joeostrander/gameboy_xl/images/IMG_4544.JPG

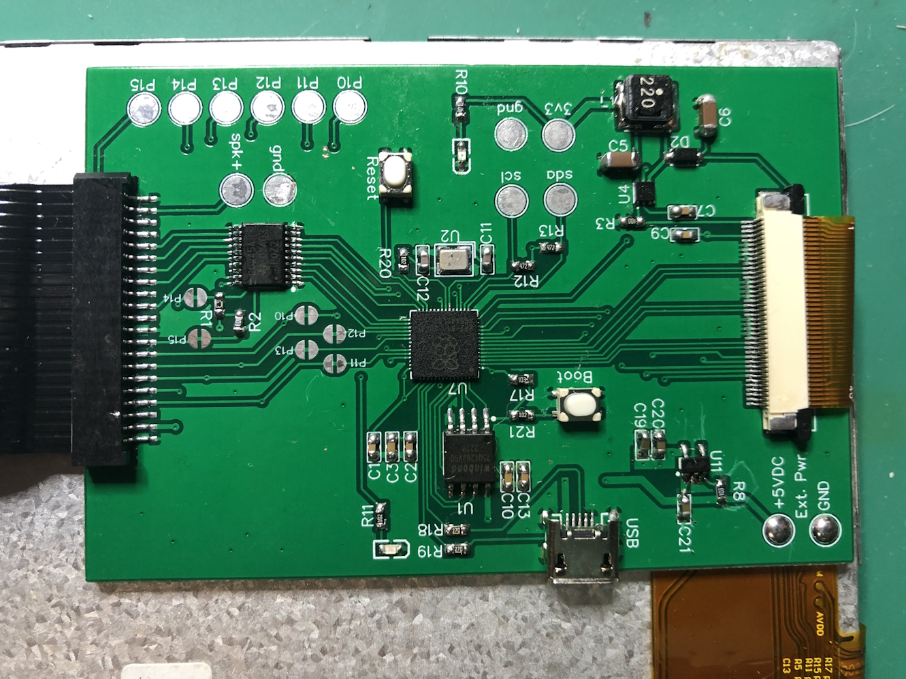
images/IMG_4544.JPG
