joeostrander/gameboy_xl/images/IMG_4554.JPG

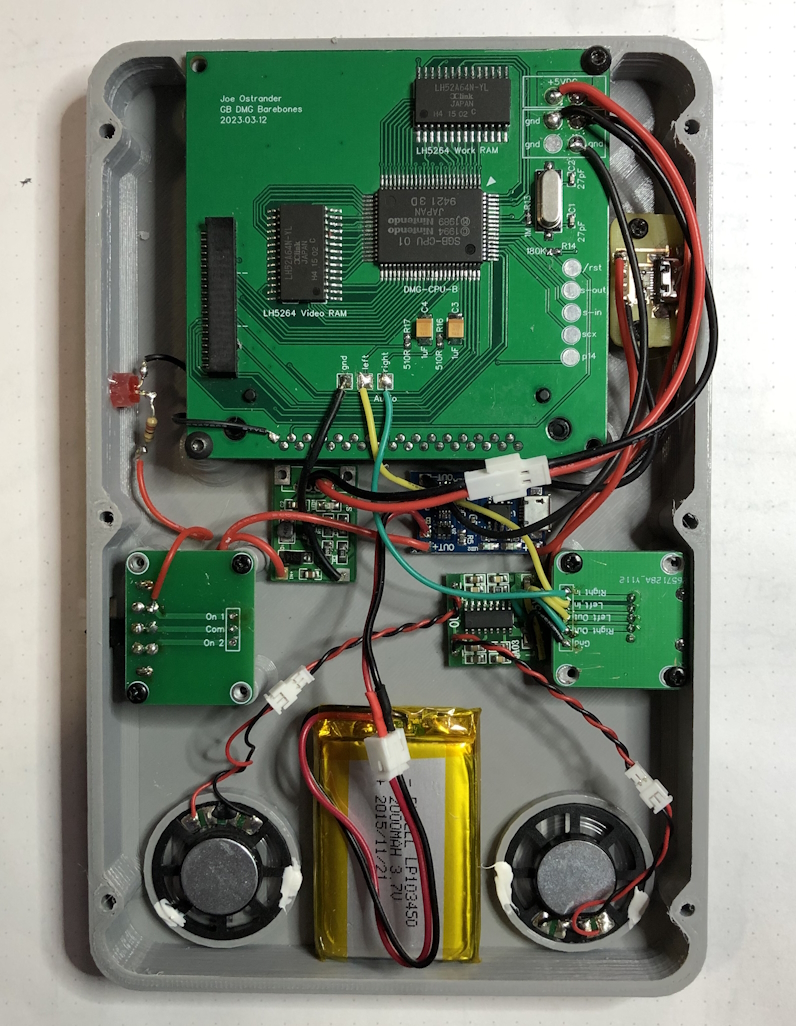
images/IMG_4554.JPG
