joeostrander/gameboy_xl/images/IMG_4557.JPG

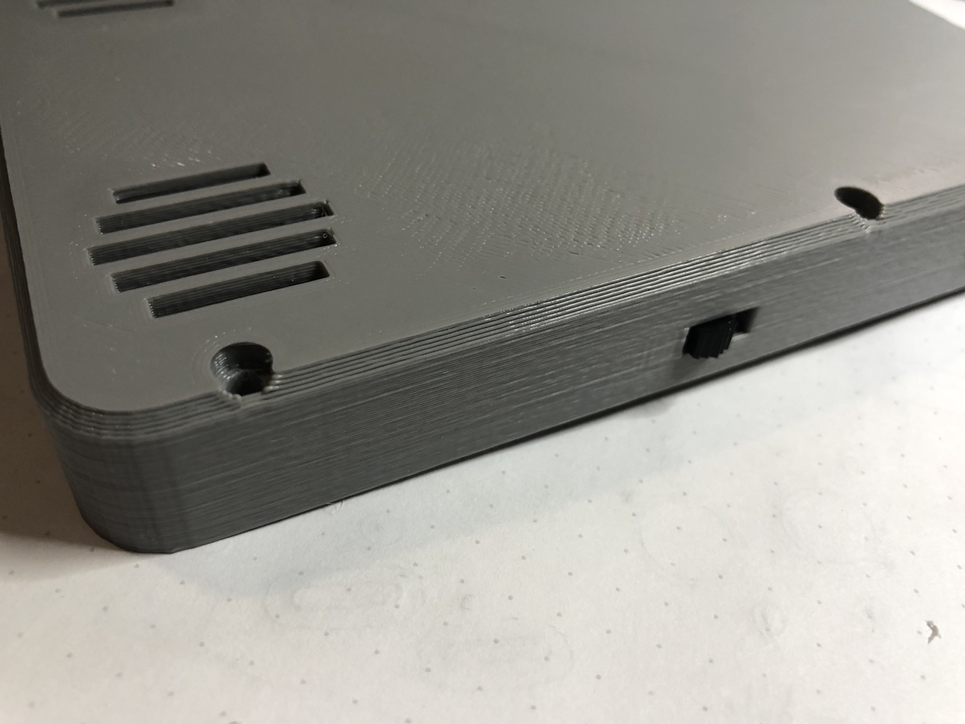
images/IMG_4557.JPG
