joeostrander/gameboy_xl/images/IMG_4558.JPG

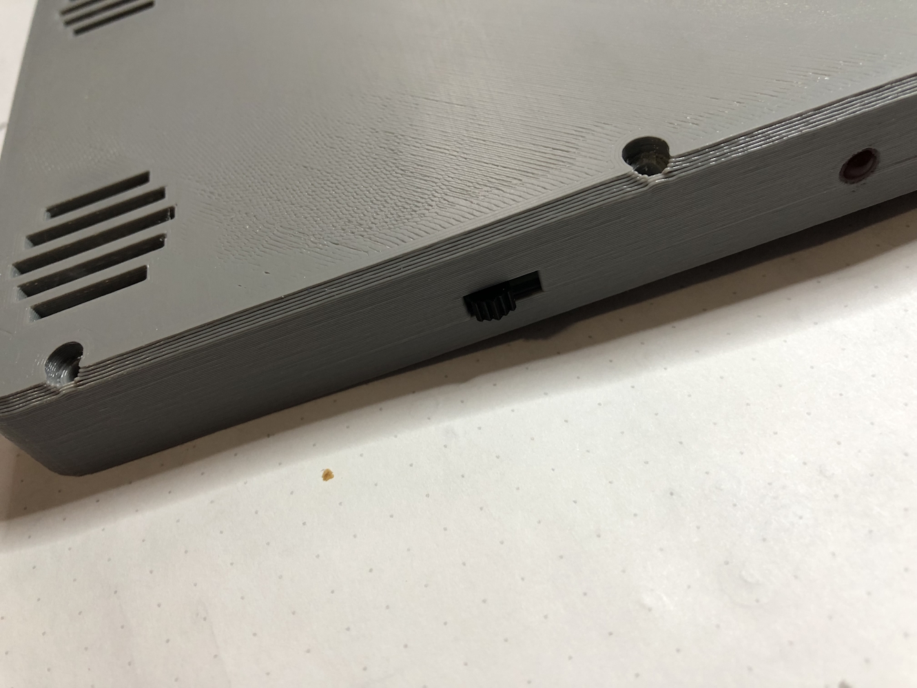
images/IMG_4558.JPG
