joeostrander/gameboy_xl/images/IMG_4560.JPG

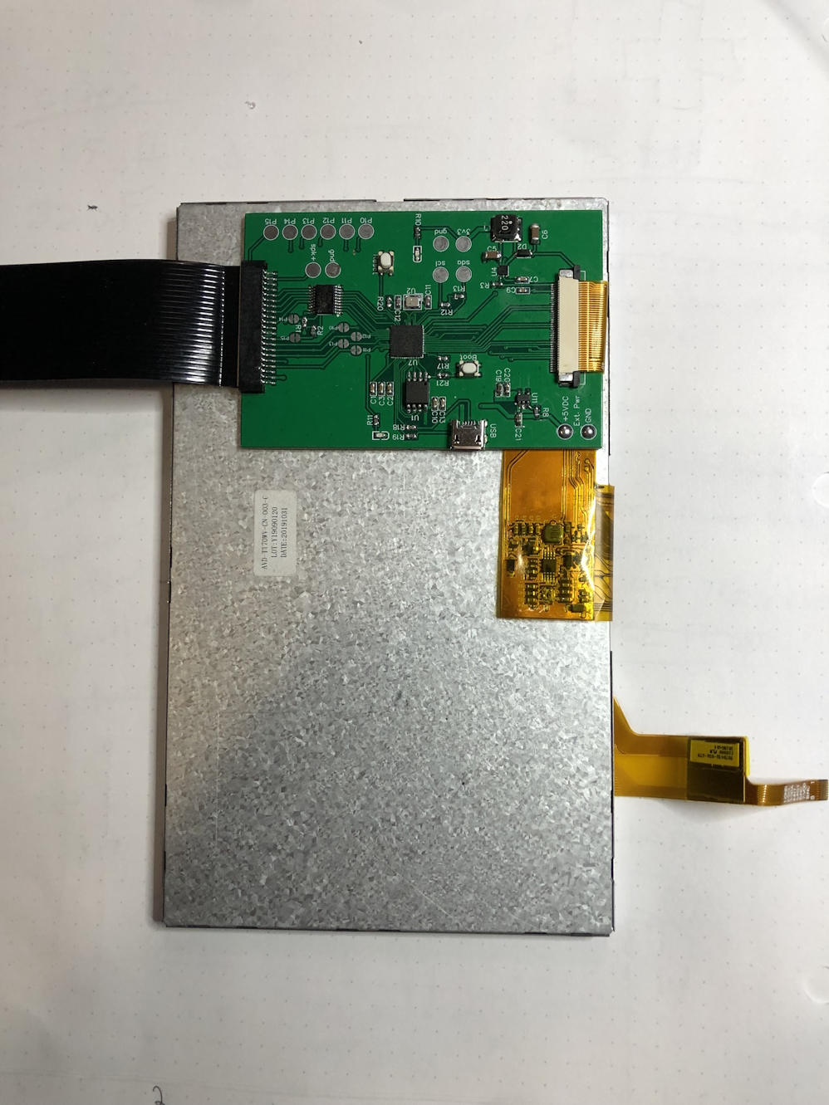
images/IMG_4560.JPG
