joeostrander/gameboy_xl/images/IMG_4566.JPG

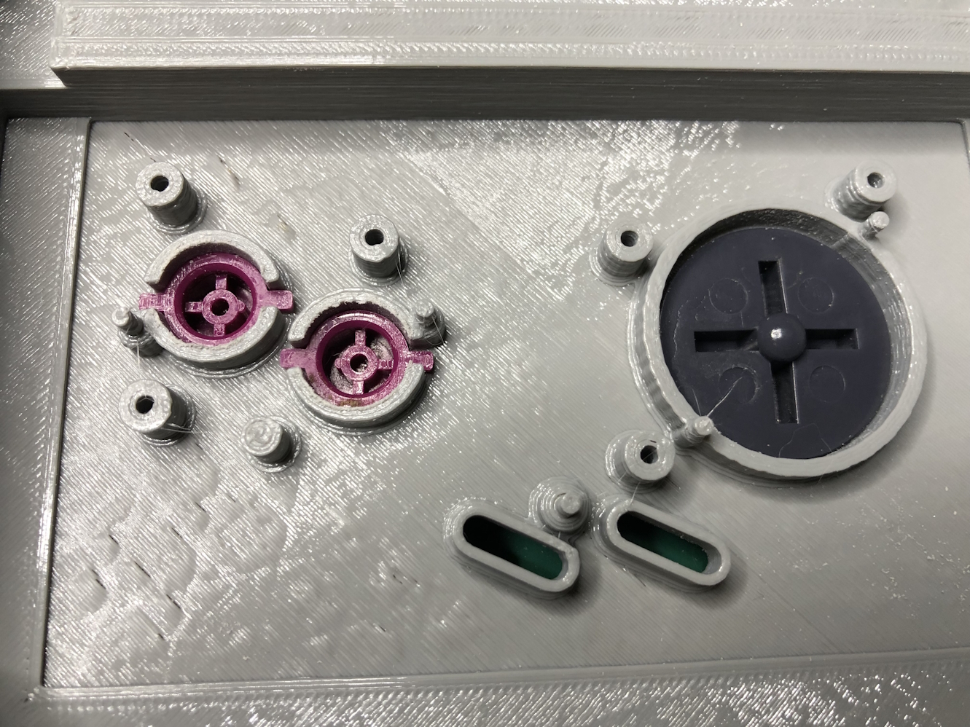
images/IMG_4566.JPG
