joeostrander/gameboy_xl/images/IMG_4568.JPG

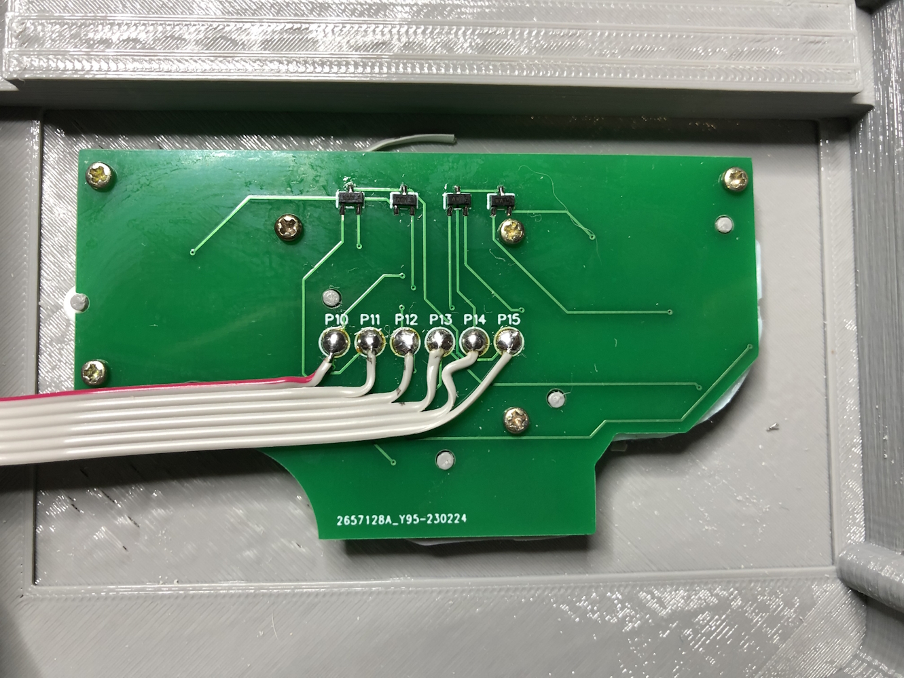
images/IMG_4568.JPG
