joeostrander/gameboy_xl/images/IMG_4569.JPG

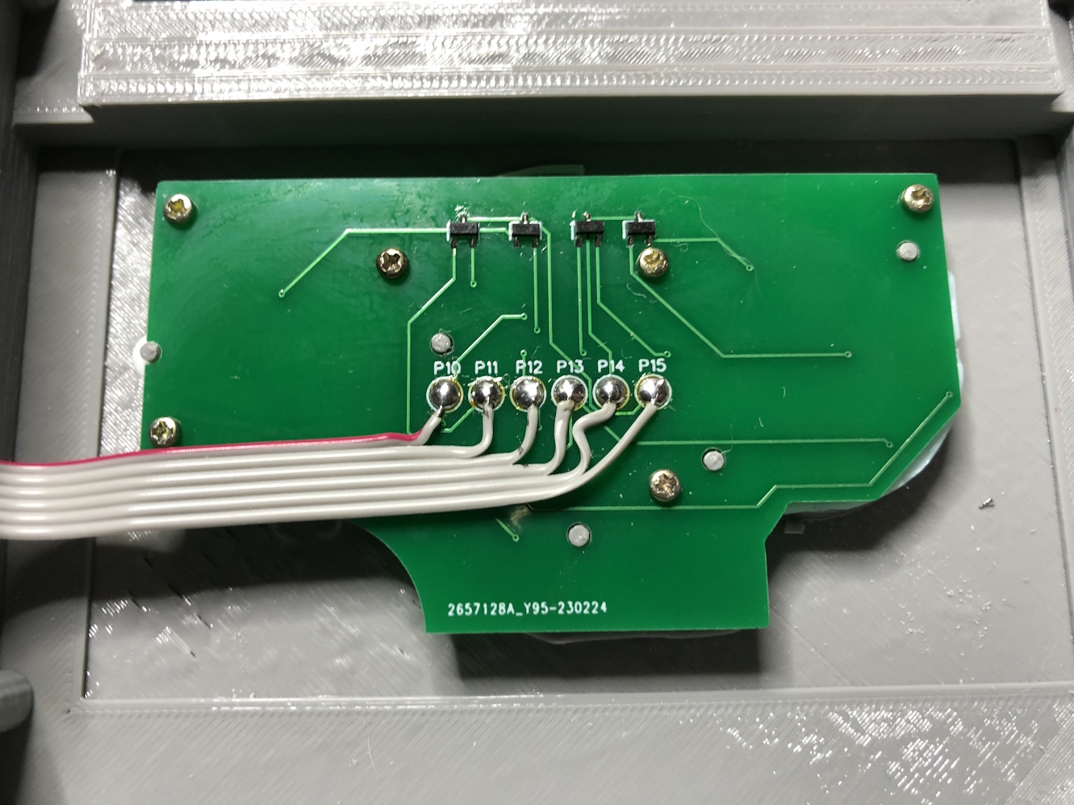
images/IMG_4569.JPG
