joeostrander/gameboy_xl/images/IMG_4572.JPG

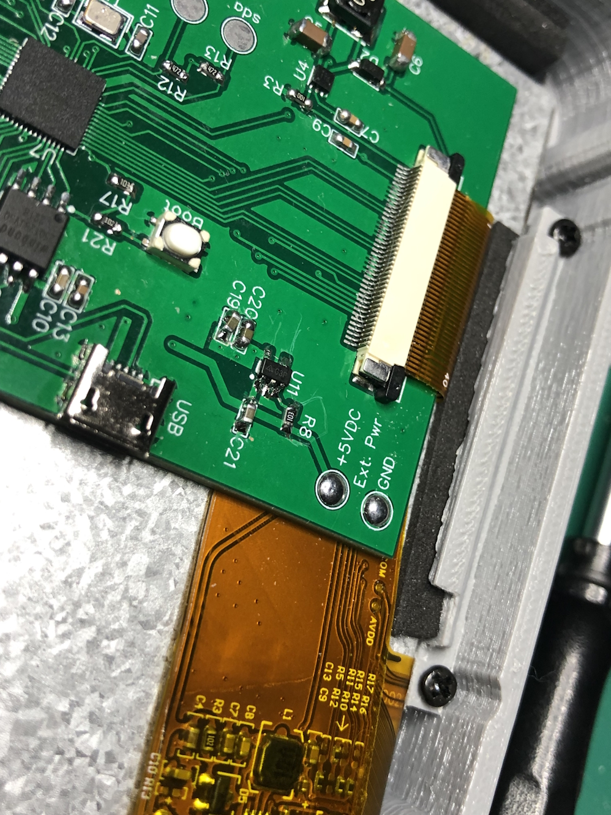
images/IMG_4572.JPG
