joeostrander/gameboy_xl/images/IMG_4573.JPG

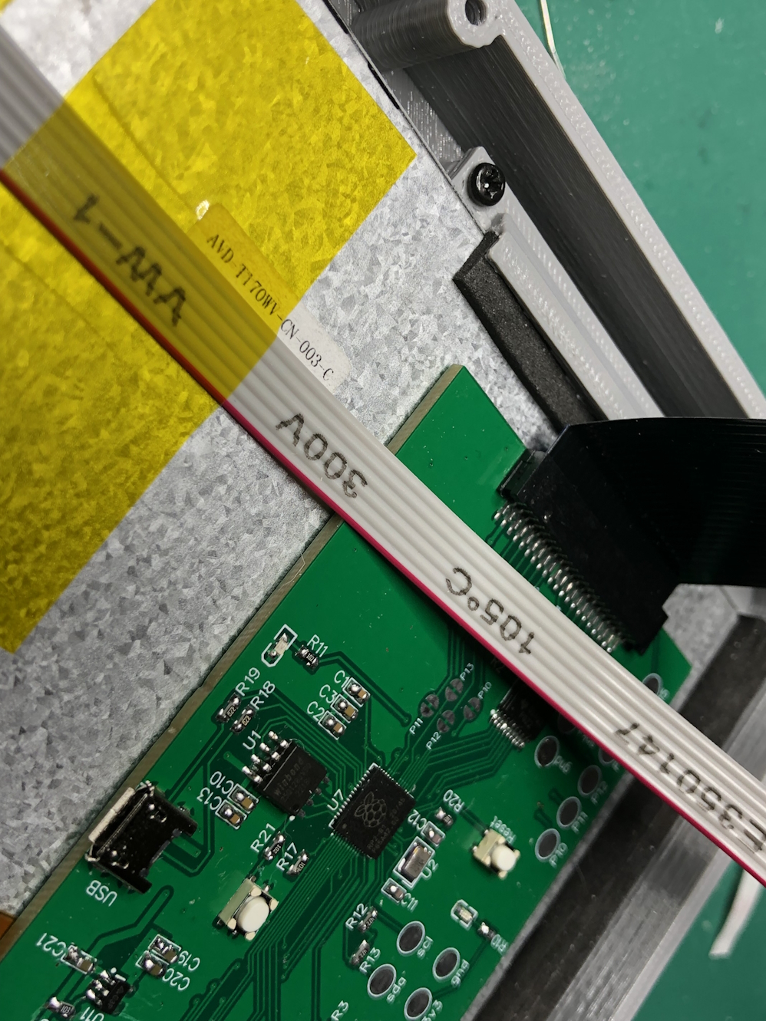
images/IMG_4573.JPG
