joeostrander/gameboy_xl/images/IMG_4574.JPG

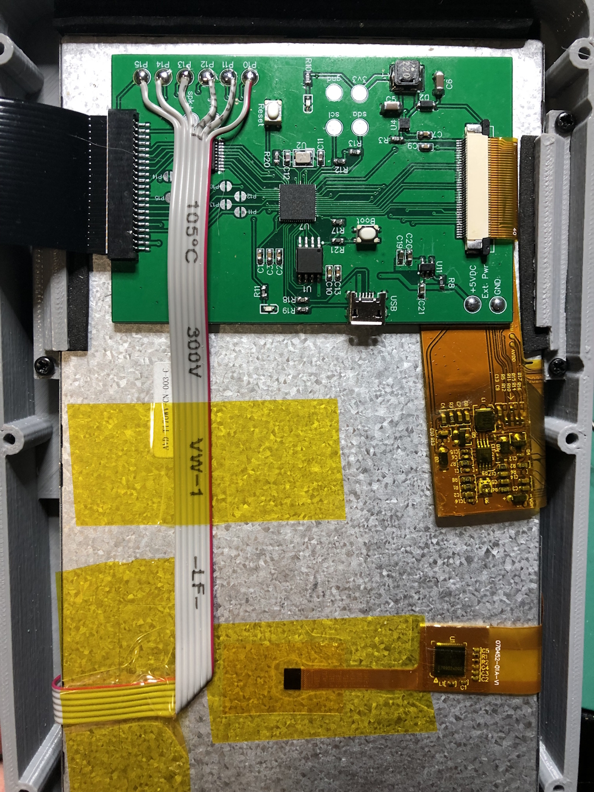
images/IMG_4574.JPG
