joeostrander/gameboy_xl/images/IMG_4575.JPG

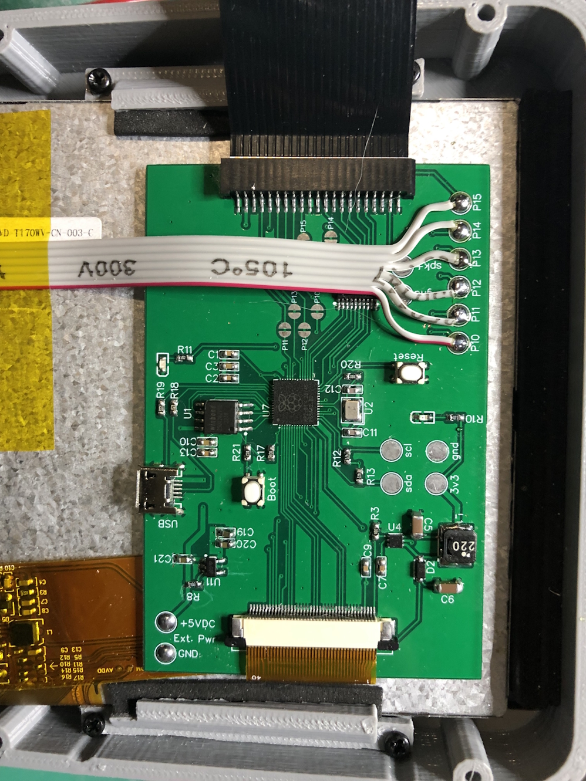
images/IMG_4575.JPG
