joeostrander/gameboy_xl/images/IMG_4580.JPG

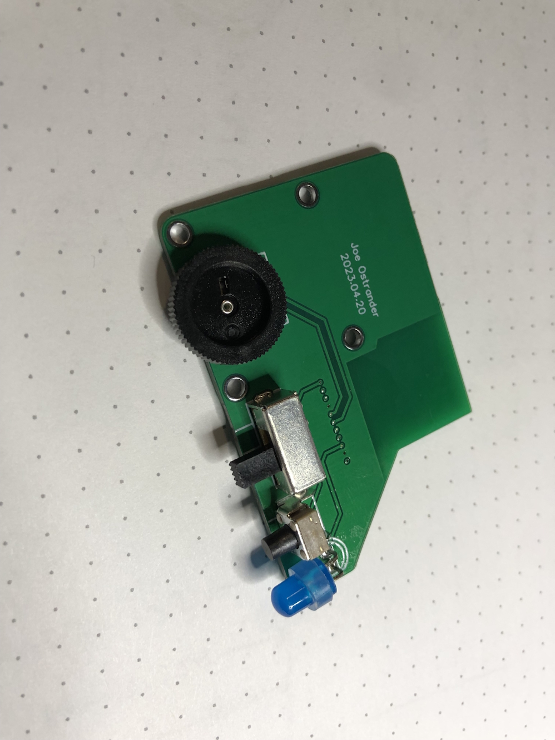
images/IMG_4580.JPG
