joeostrander/gameboy_xl/images/IMG_4581.JPG

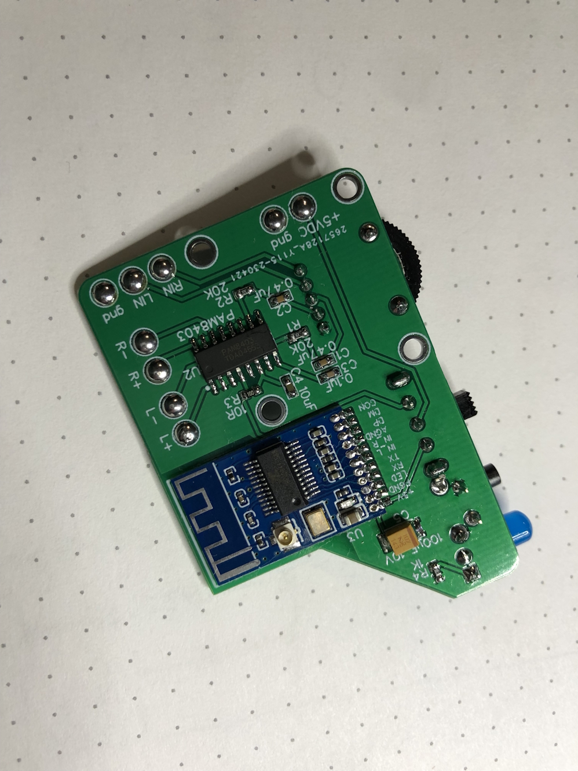
images/IMG_4581.JPG
