joeostrander/gameboy_xl/images/IMG_4582.JPG

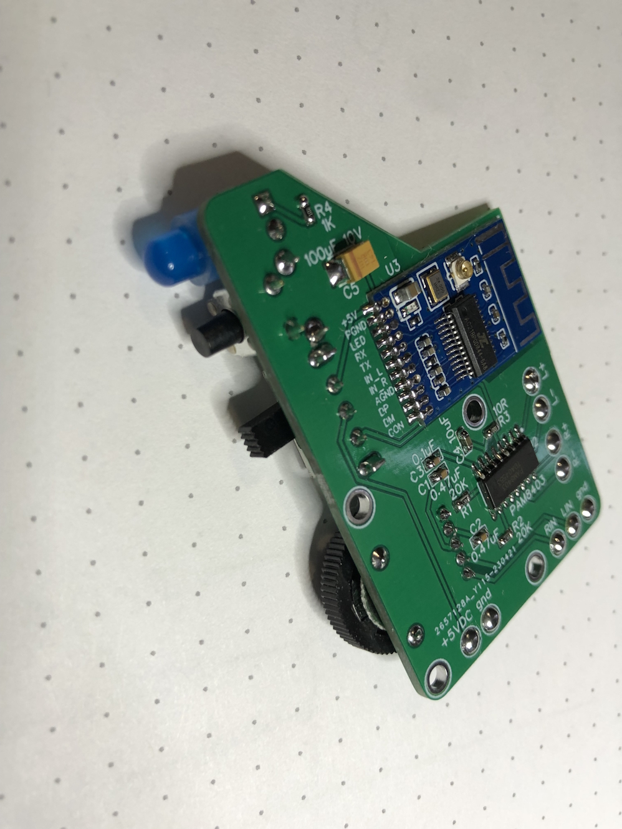
images/IMG_4582.JPG
