joeostrander/gameboy_xl/images/IMG_4587.JPG

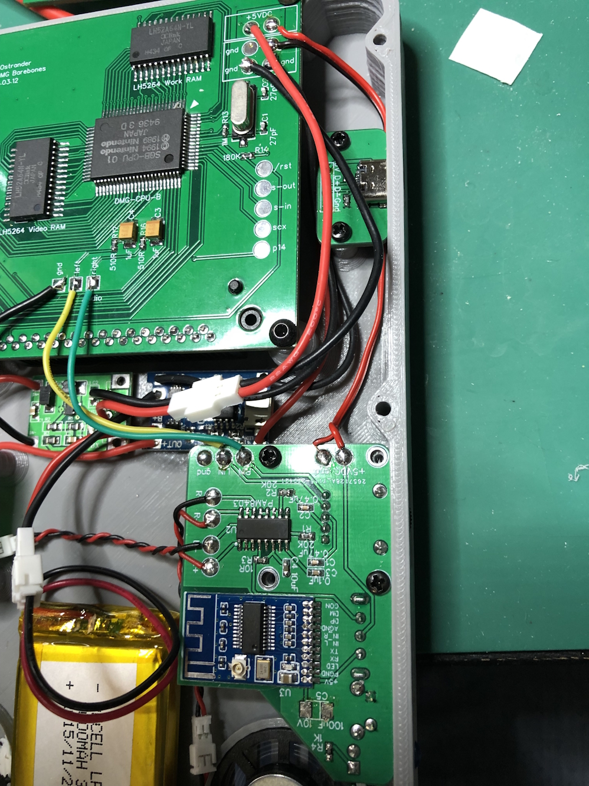
images/IMG_4587.JPG
