joeostrander/gameboy_xl/images/IMG_4588.JPG

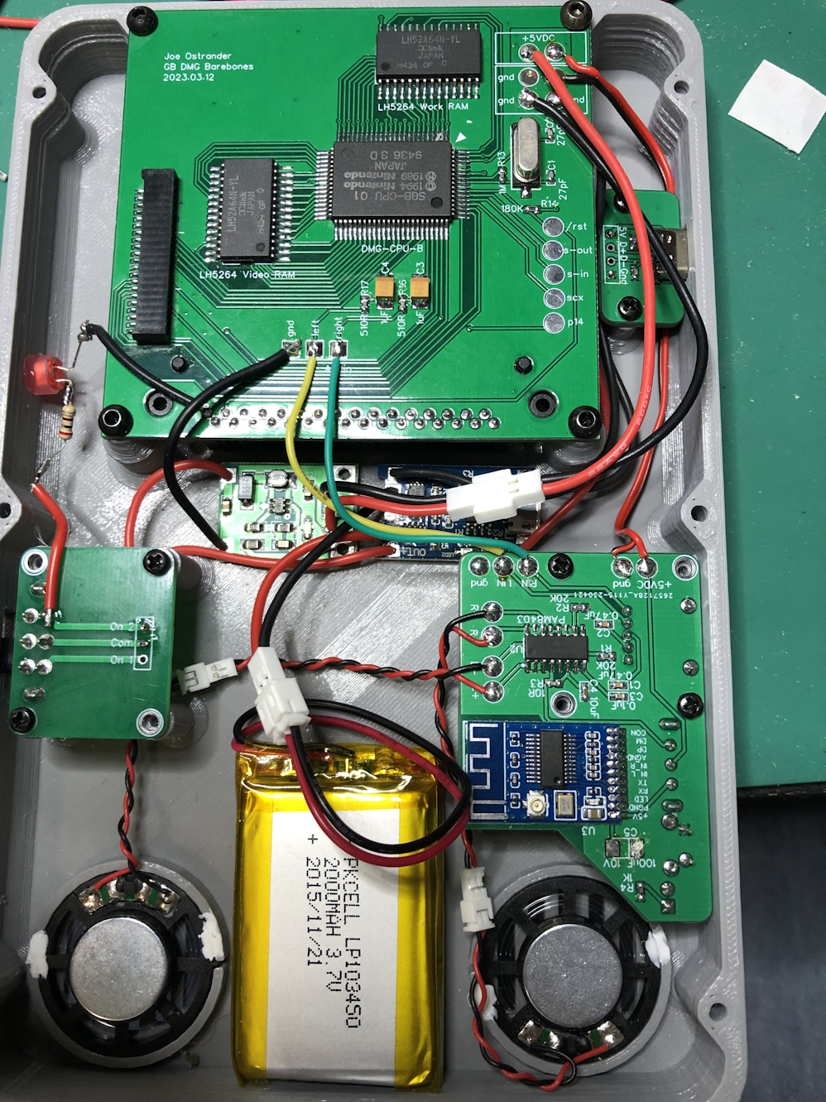
images/IMG_4588.JPG
