joeostrander/gameboy_xl/images/IMG_4589.JPG

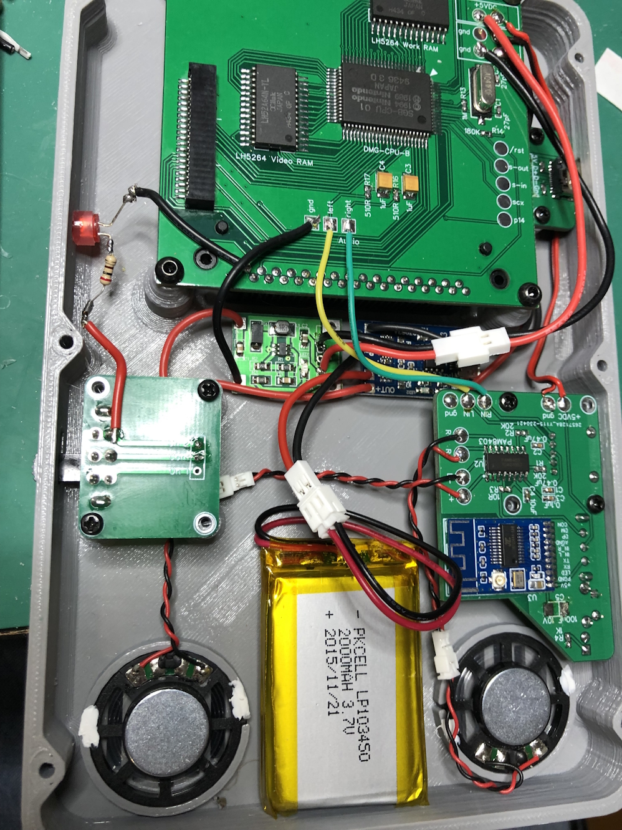
images/IMG_4589.JPG
