joeostrander/gameboy_xl/images/IMG_4590.JPG

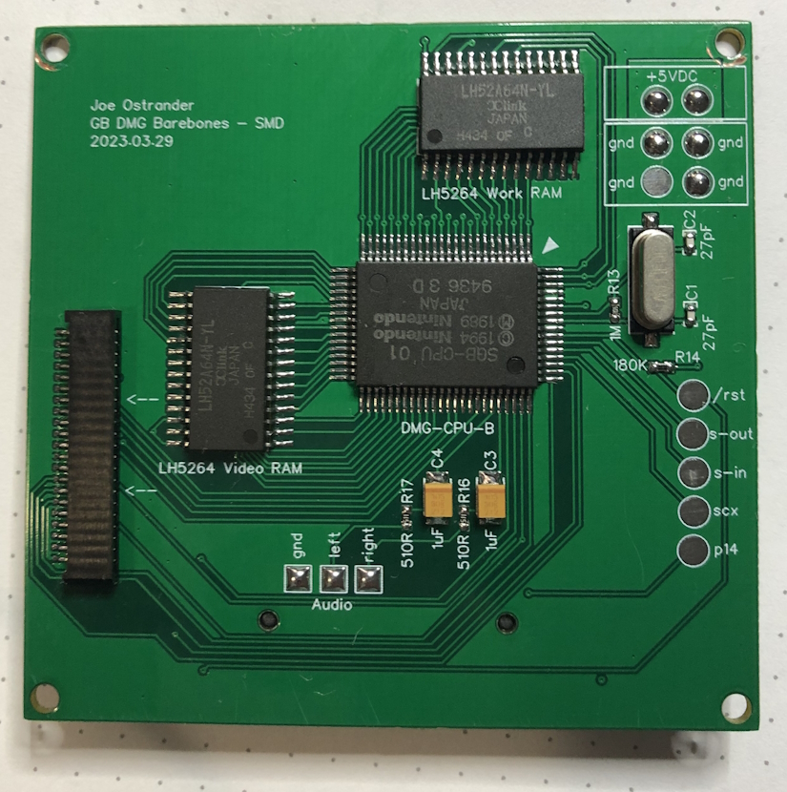
images/IMG_4590.JPG
