joeostrander/gameboy_xl/images/IMG_4591.JPG

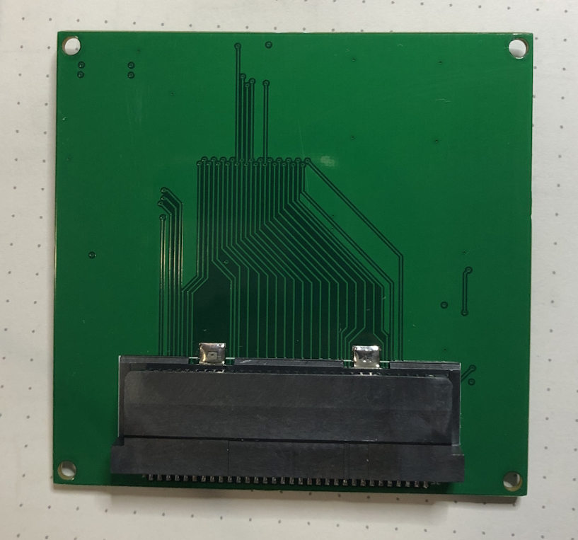
images/IMG_4591.JPG
