joeostrander/gameboy_xl/images/IMG_4592.JPG

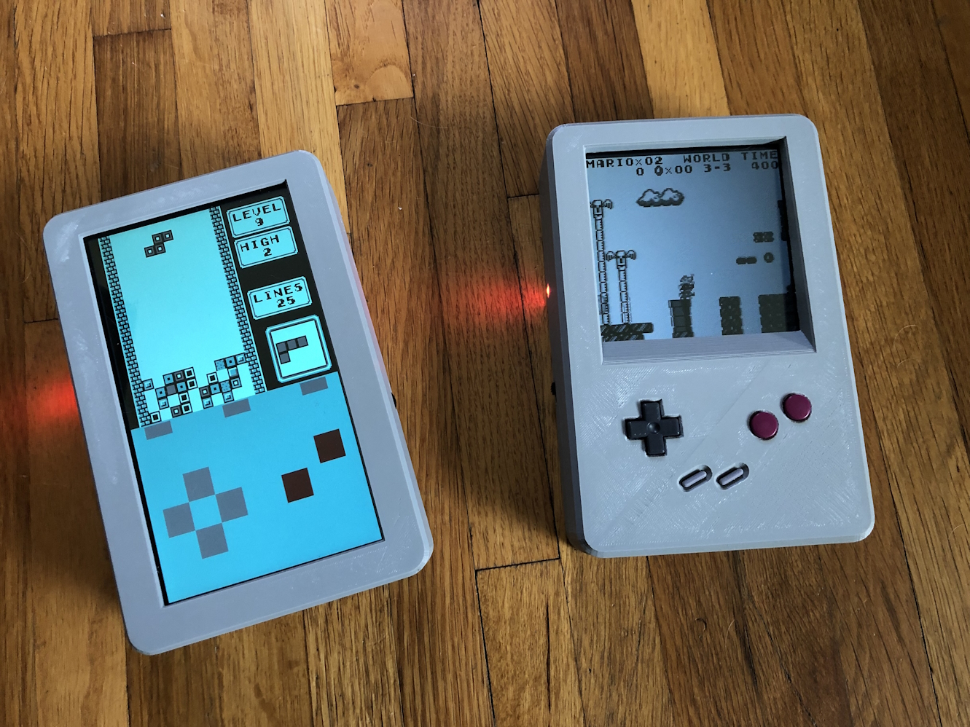
images/IMG_4592.JPG
