joeostrander/gameboy_xl/images/IMG_4593.JPG

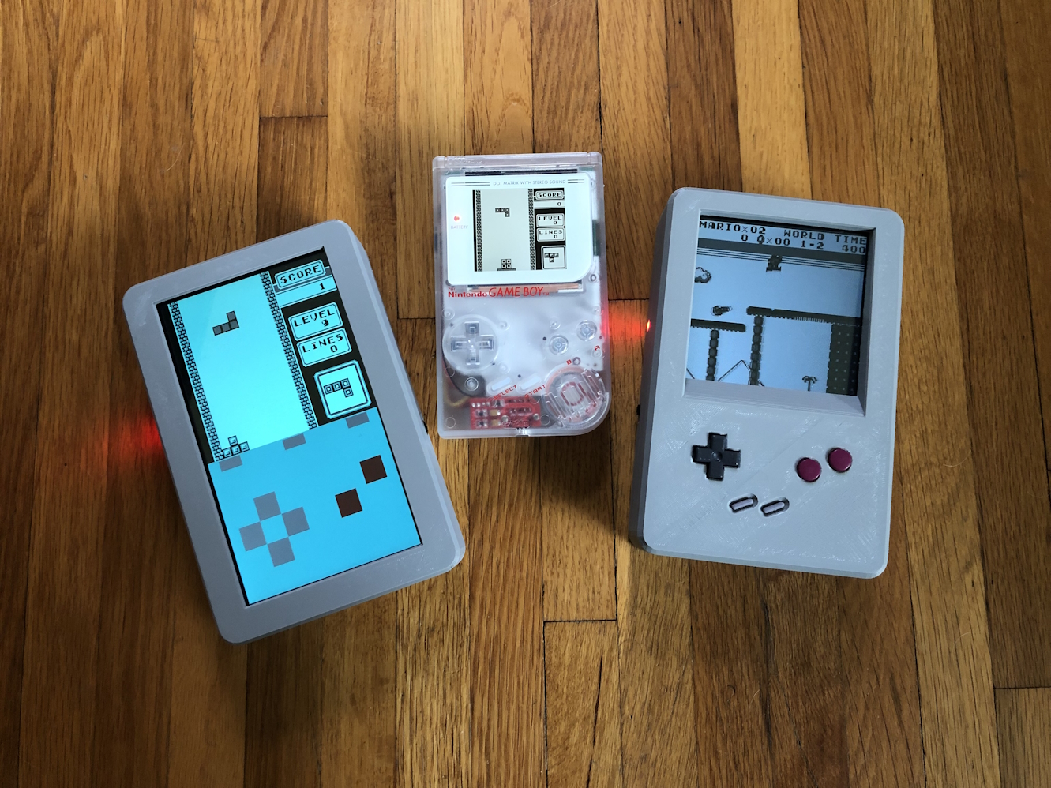
images/IMG_4593.JPG
