joeostrander/gameboy_xl/images/IMG_4595.JPG

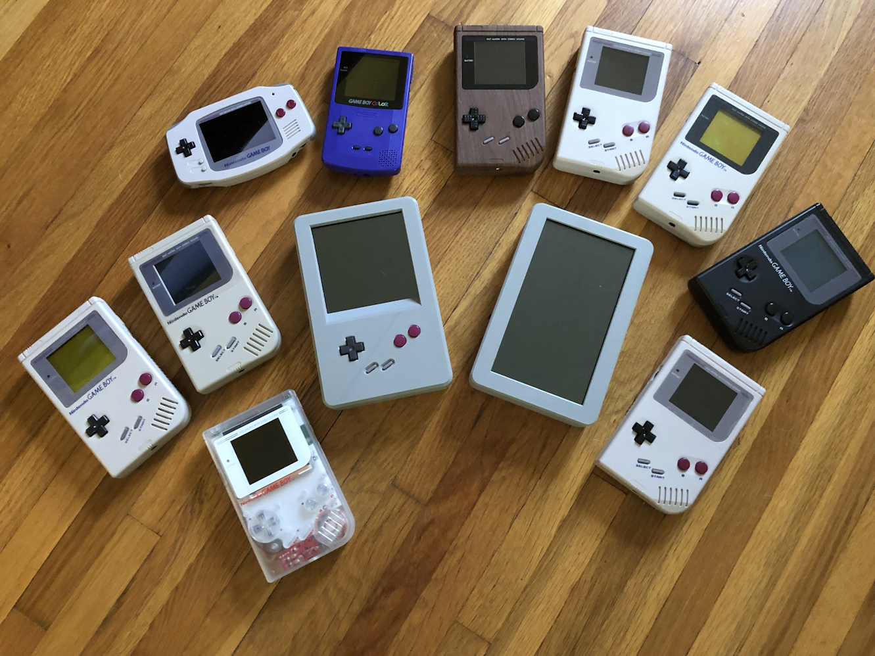
images/IMG_4595.JPG
