joeostrander/gameboy_xl/images/IMG_4875.JPG

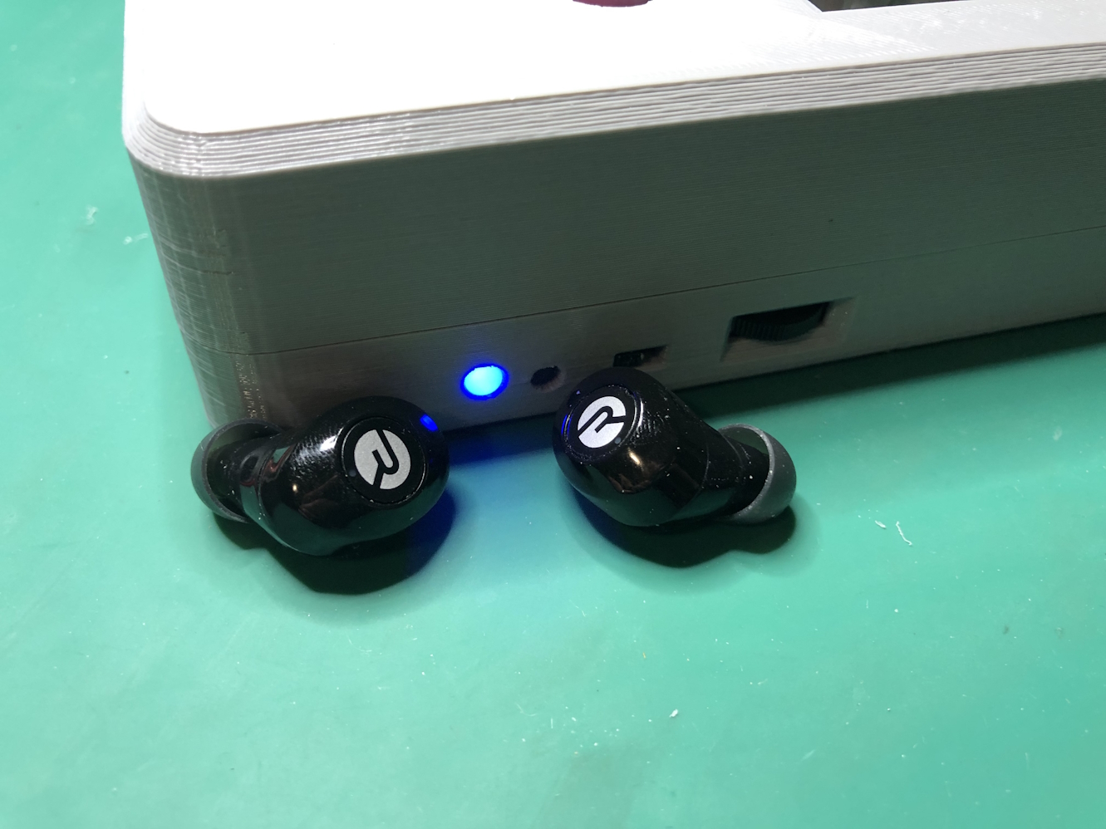
images/IMG_4875.JPG
