joeostrander/gameboy_xl/images/IMG_4876.JPG

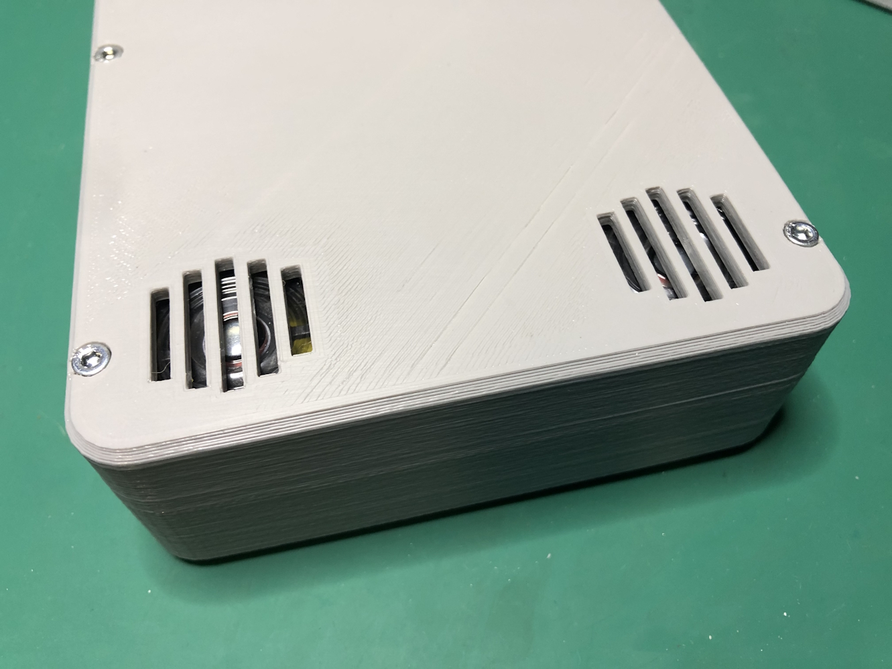
images/IMG_4876.JPG
