joeostrander/gameboy_xl/images/IMG_E4554.JPG

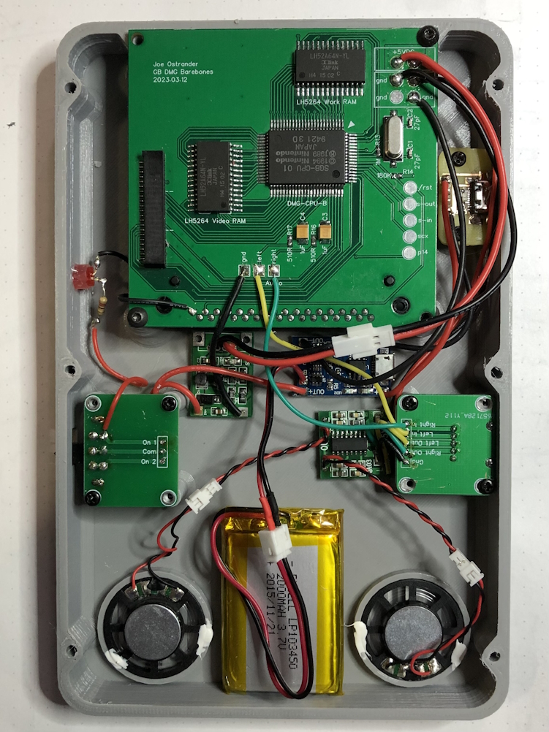
images/IMG_E4554.JPG
