joeostrander/gameboy_xl/images/IMG_E4560.JPG

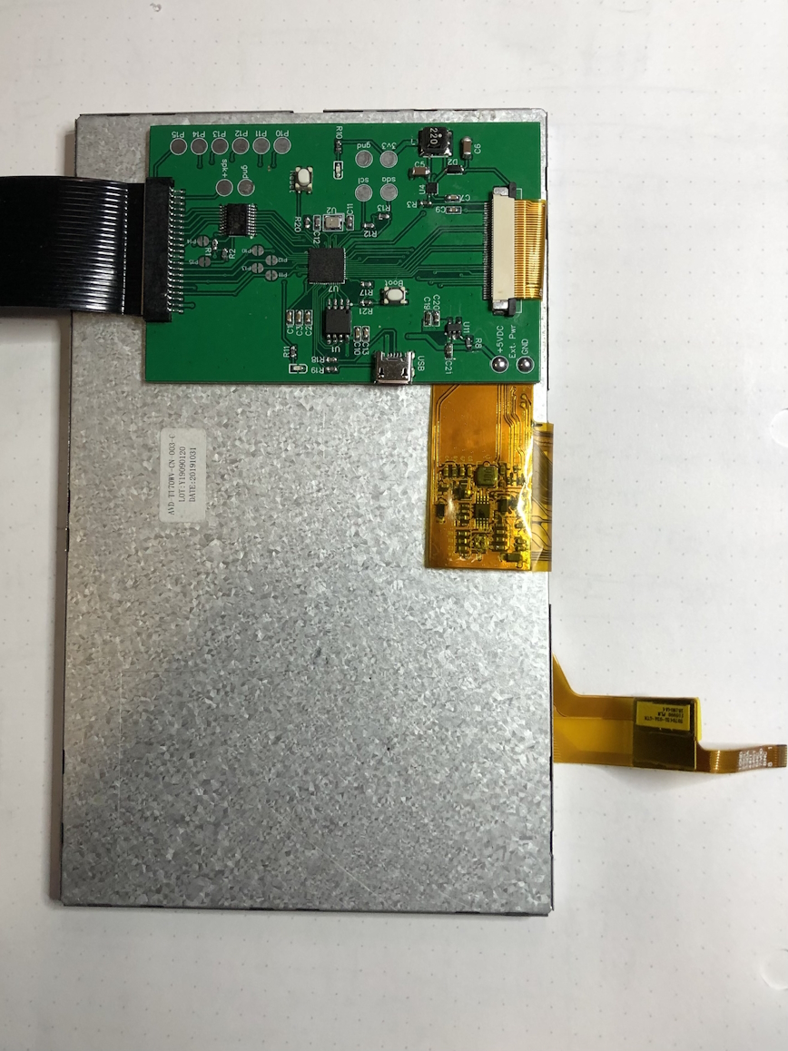
images/IMG_E4560.JPG
