joeostrander/gameboy_xl/images/IMG_E4742.JPG

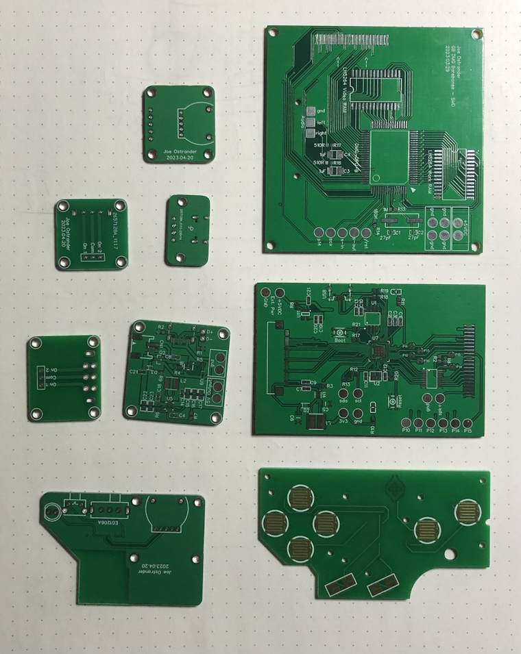
images/IMG_E4742.JPG
