joeostrander/gameboy_xl/images/IMG_E4743.JPG

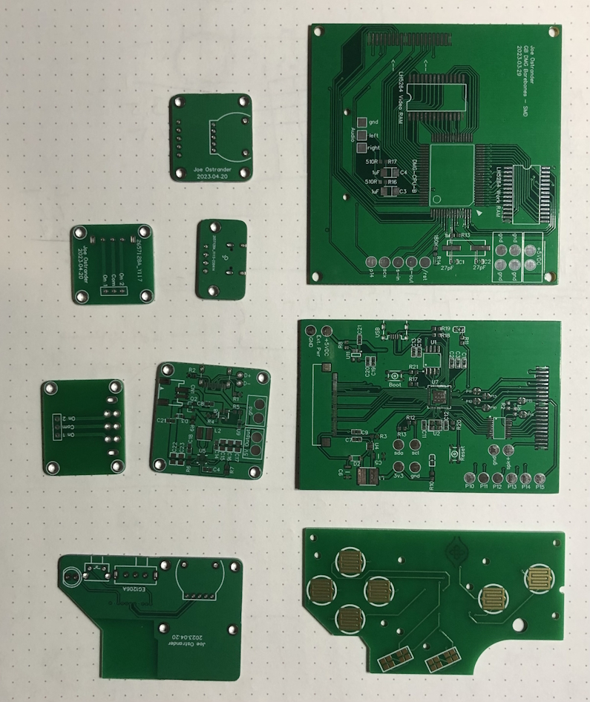
images/IMG_E4743.JPG
