joeostrander/gameboy_xl/images/IMG_E4744.JPG

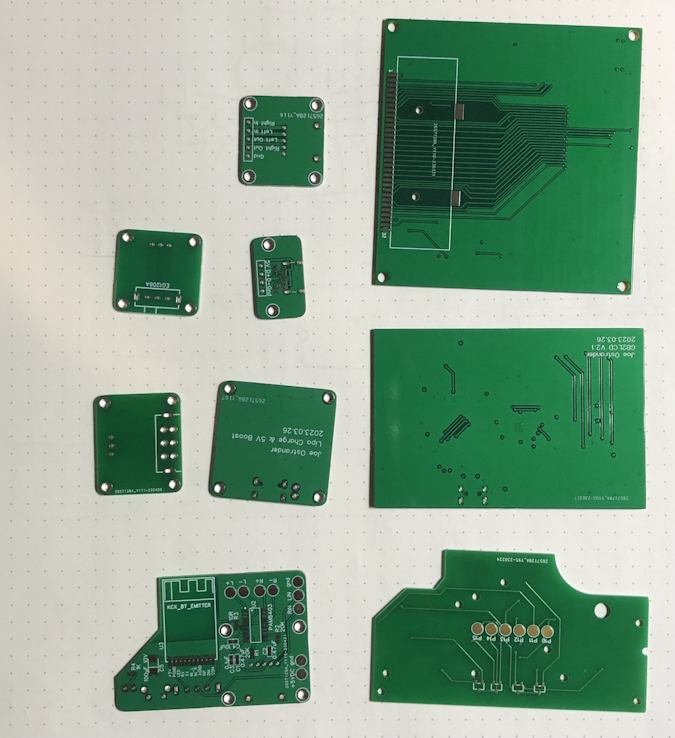
images/IMG_E4744.JPG
