joeostrander/gameboy_xl/images/IMG_E4834.JPG

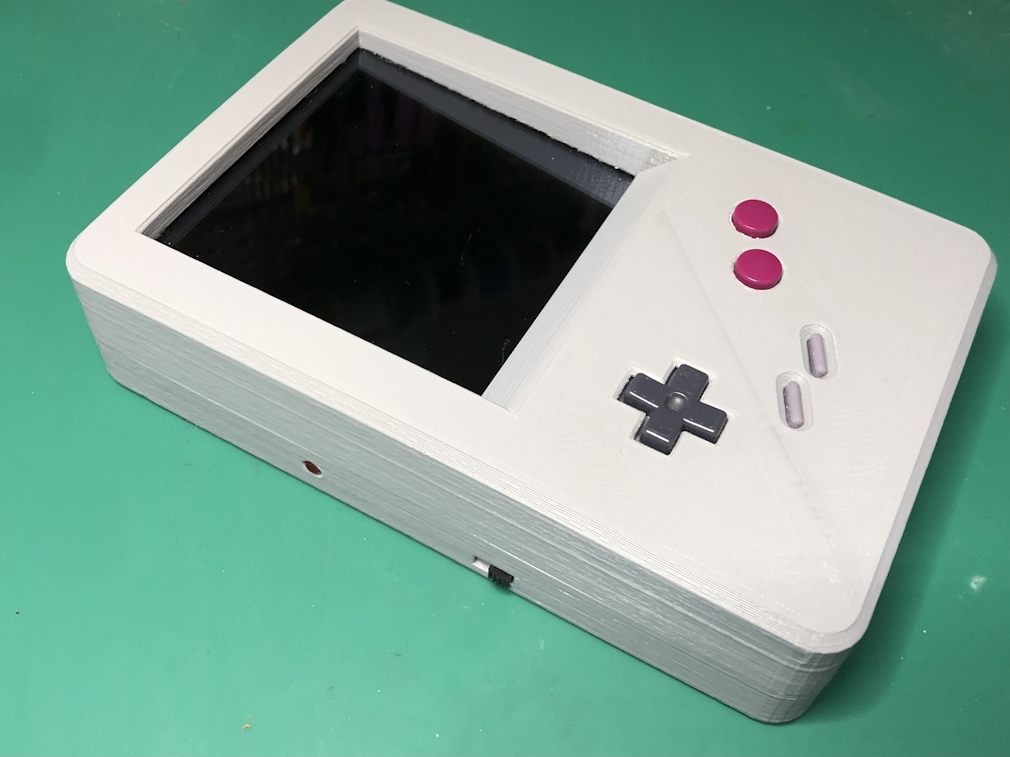
images/IMG_E4834.JPG
