joeostrander/gameboy_xl/images/IMG_E4835.JPG

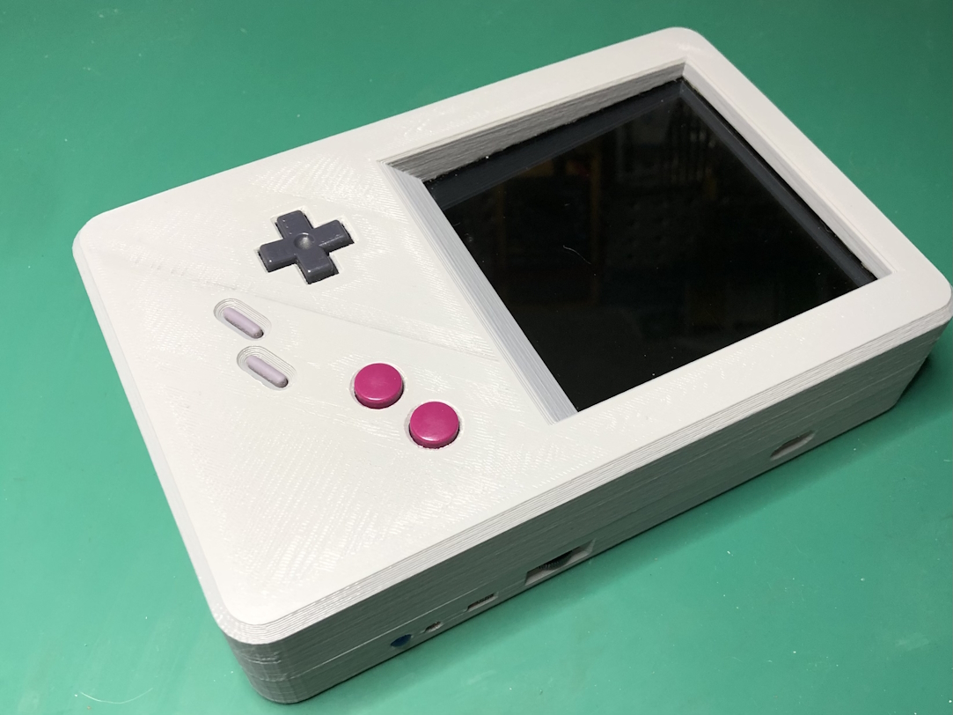
images/IMG_E4835.JPG
