joeostrander/gameboy_xl/images/IMG_E4837.JPG

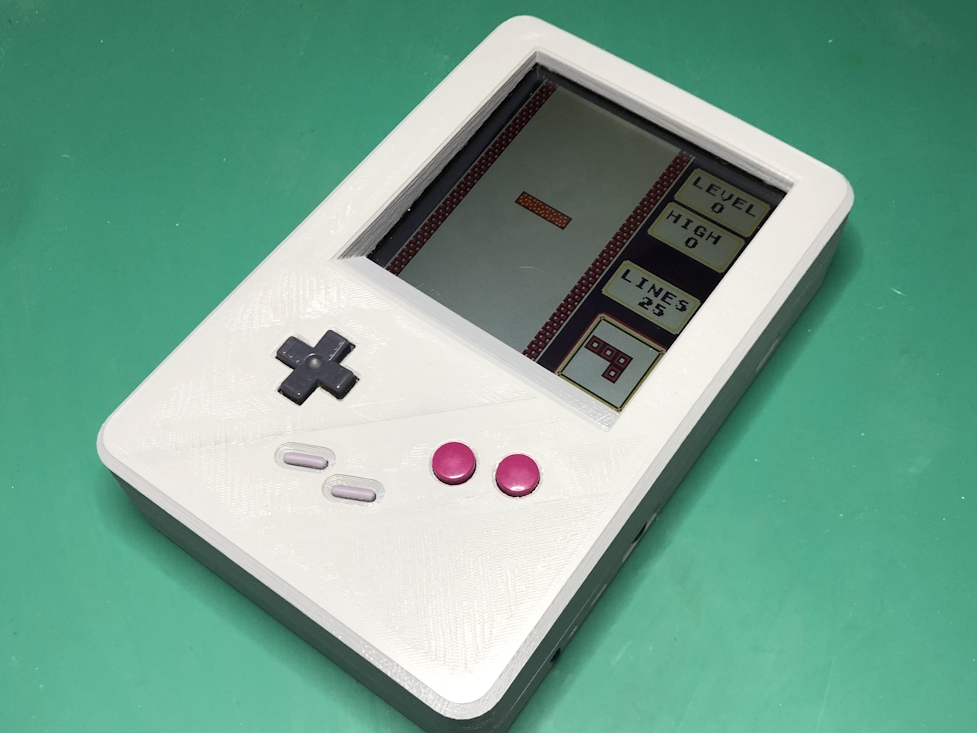
images/IMG_E4837.JPG
