joeostrander/gameboy_xl/images/IMG_E4840.JPG

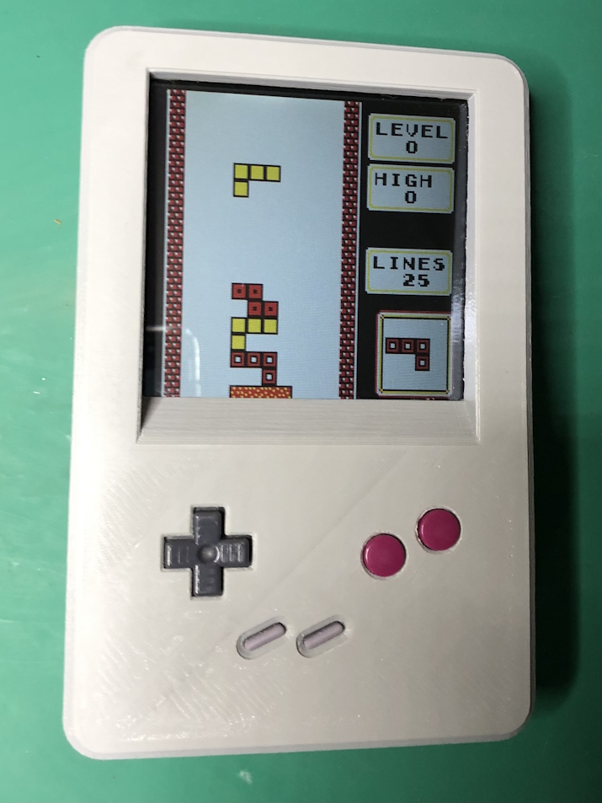
images/IMG_E4840.JPG
