joeostrander/gameboy_xl/images/IMG_E4841.JPG

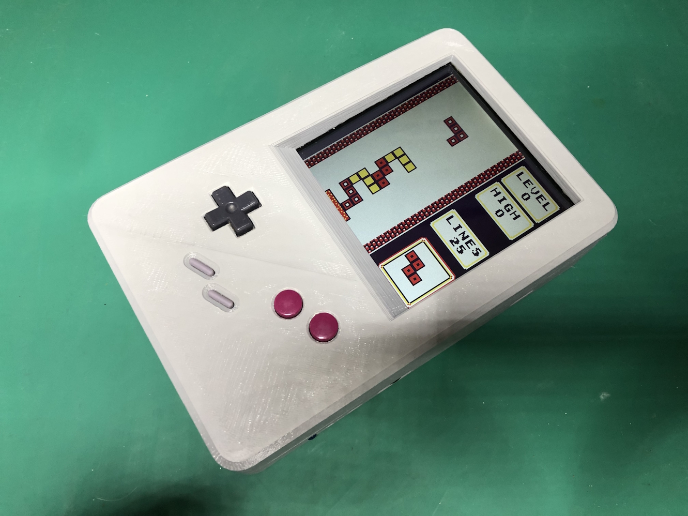
images/IMG_E4841.JPG
