joeostrander/gameboy_xl/images/IMG_E4842.JPG

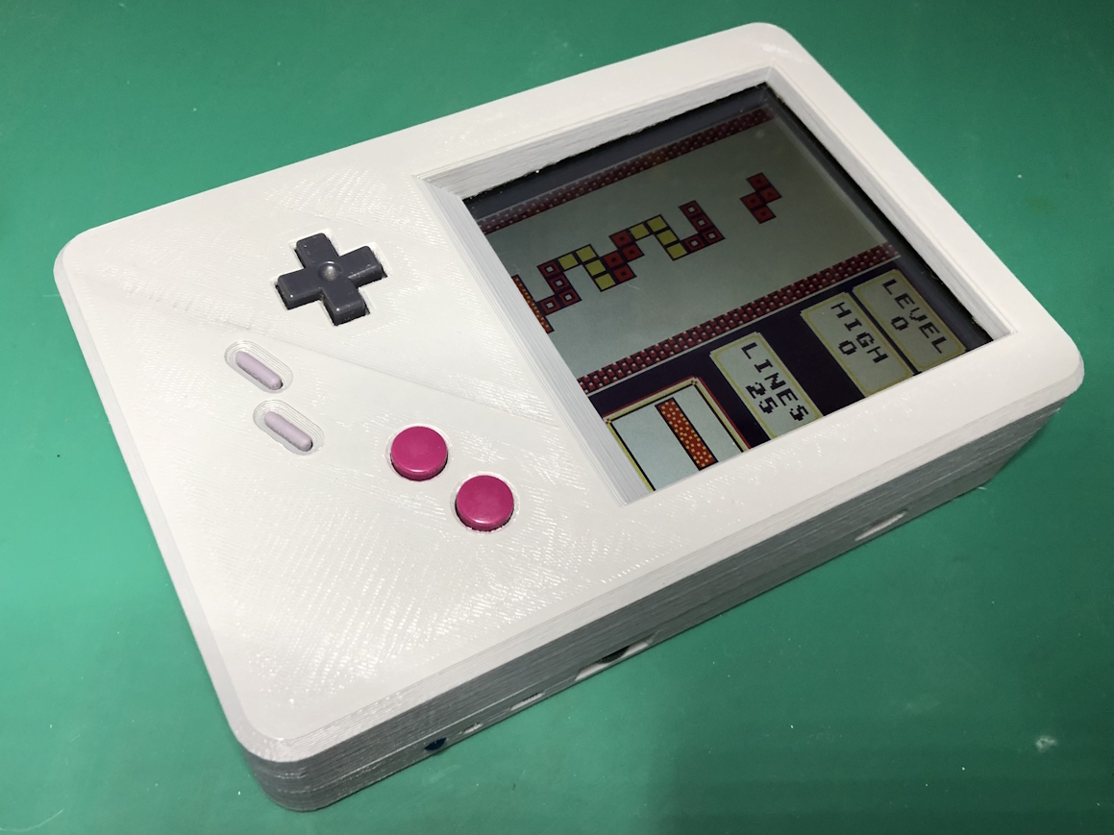
images/IMG_E4842.JPG
