joeostrander/gameboy_xl/images/IMG_E4852.JPG

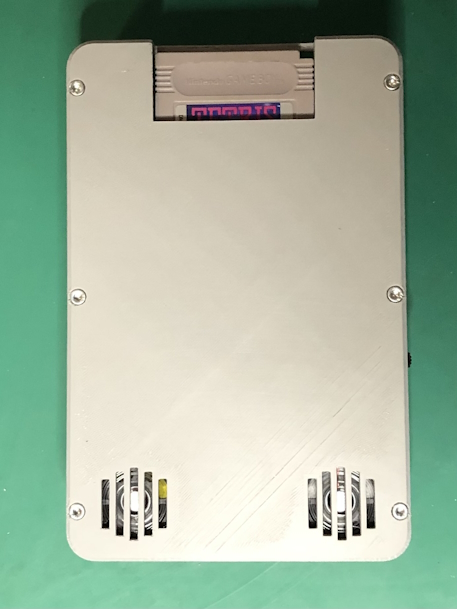
images/IMG_E4852.JPG
