joeostrander/gameboy_xl/images/IMG_E4853.JPG

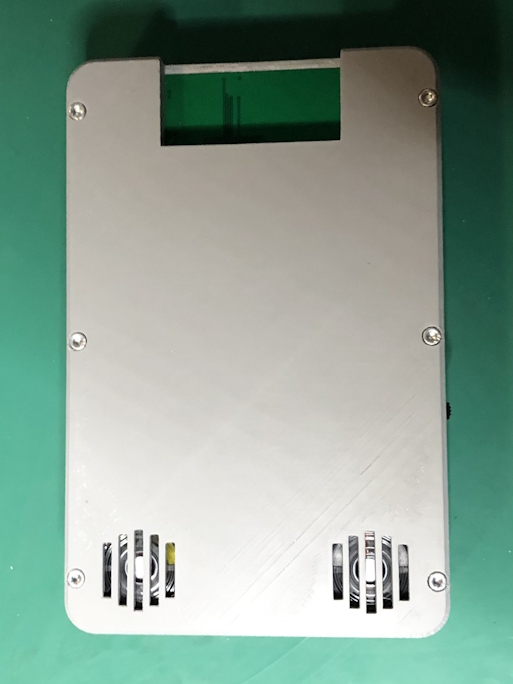
images/IMG_E4853.JPG
