joeostrander/gameboy_xl/images/touch1.JPG

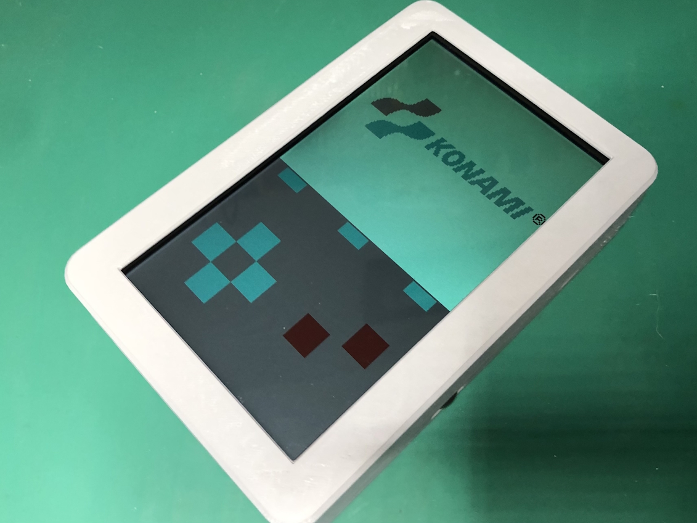
images/touch1.JPG
