joeostrander/gameboy_xl/images/touch_case_back_game.JPG

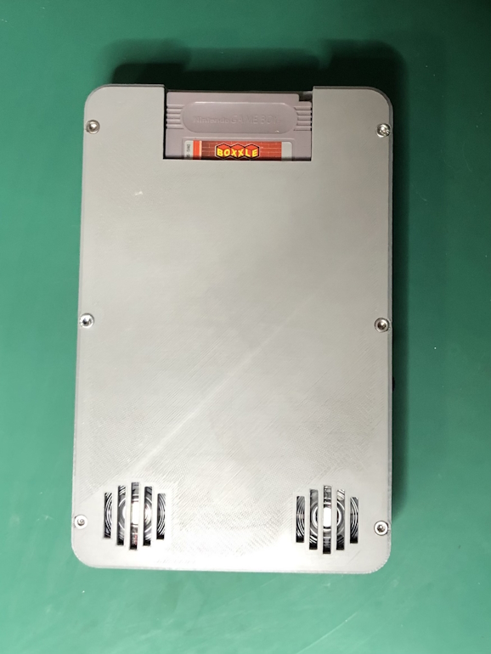
images/touch_case_back_game.JPG
