joeostrander/gameboy_xl/images/touch_osd.JPG

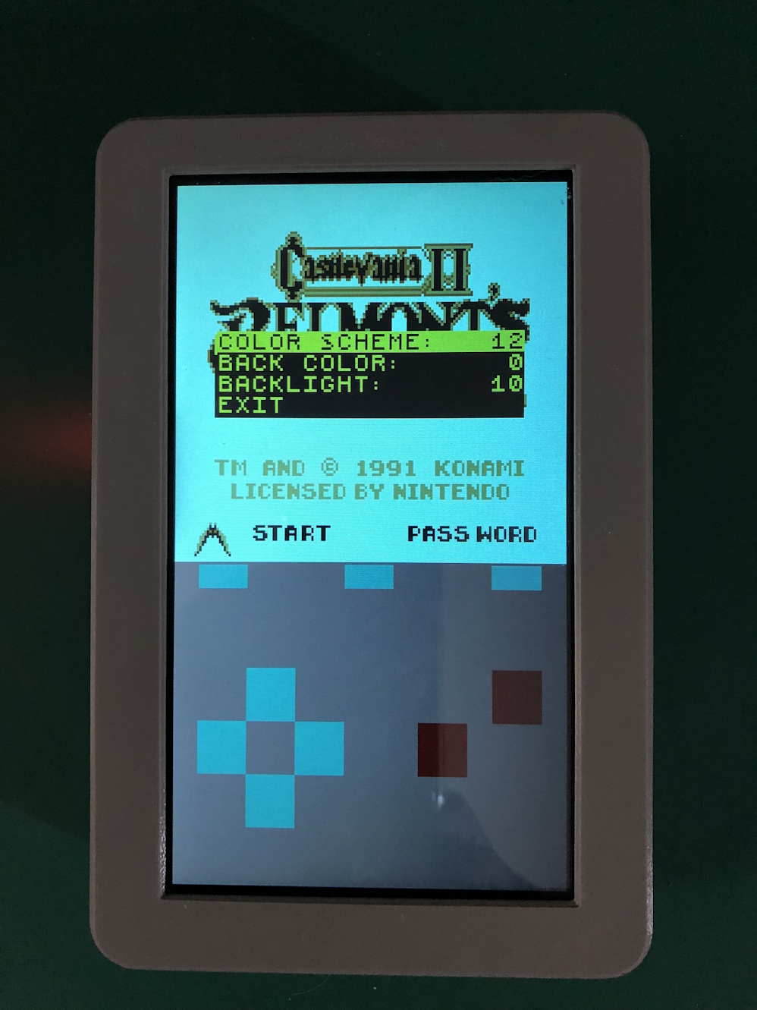
images/touch_osd.JPG
