joeostrander/gameboy_xl/images/touch_top1.JPG

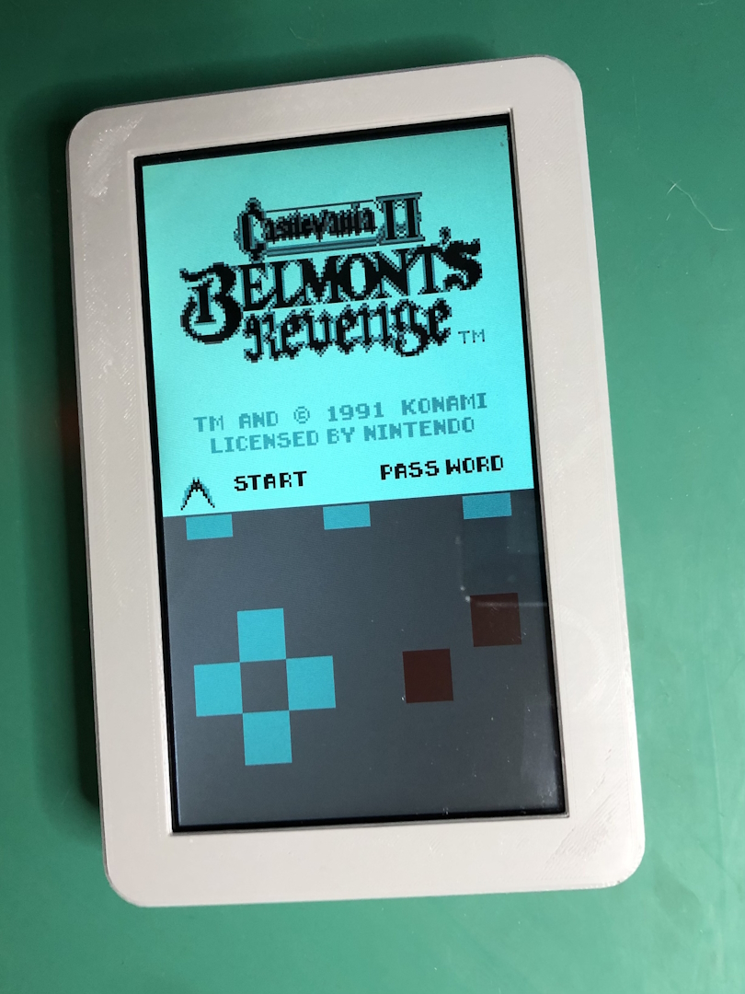
images/touch_top1.JPG
