joeostrander/gameboy_xl/images/touch_top_alt2.JPG

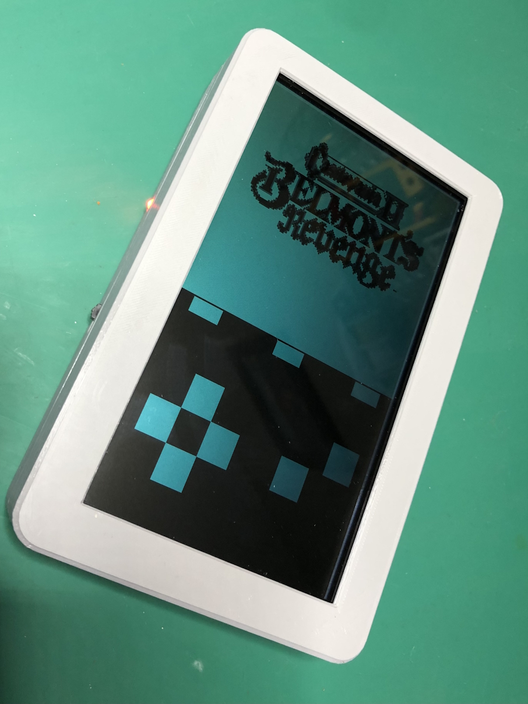
images/touch_top_alt2.JPG
