joeostrander/gameboy_xl/images/touch_top_alt_controls.JPG

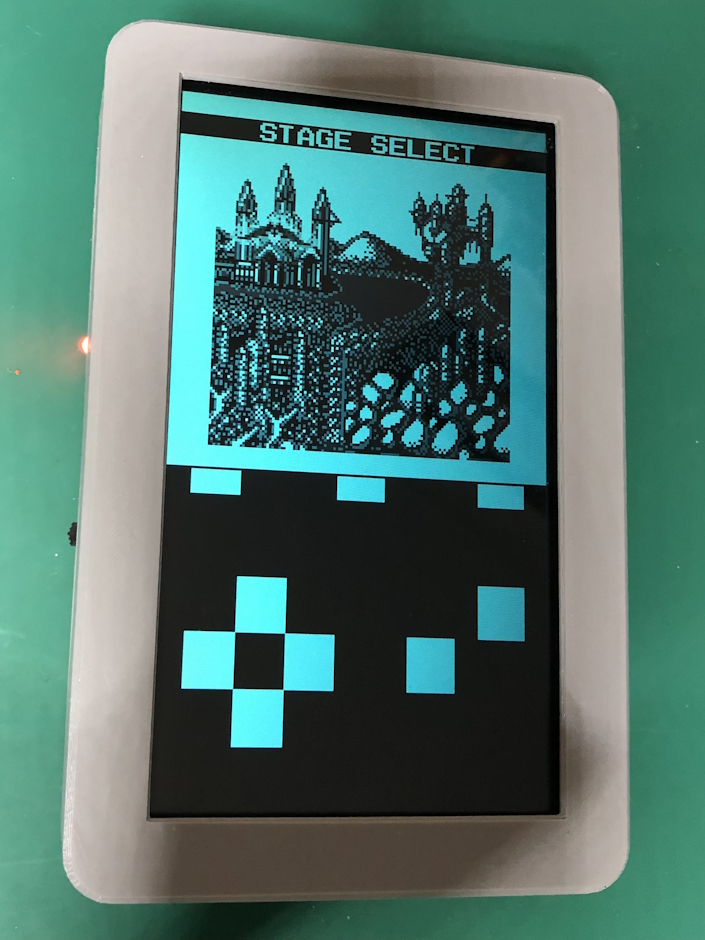
images/touch_top_alt_controls.JPG
