joeostrander/gameboy_xl/code/non-touch/osd.c

#include "osd.h"
#include <string.h>
#include <stdint.h>

static uint8_t osd_pixel_buff[OSD_CHARS_PER_LINE];   // TODO:  OSD_get_pixel_buff?
static char osd_text[OSD_LINES][OSD_CHARS_PER_LINE+1];
static bool osd_enabled = false;
static int active_line = 0;
//static uint8_t* framebuffer = NULL;
static uint8_t framebuffer[OSD_HEIGHT*OSD_WIDTH] = {0};

typedef struct 
{
    char osd_char;
    uint8_t data[OSD_CHAR_HEIGHT];
} osd_char_data_t;

//TODO: add more!
static osd_char_data_t osd_letters[] = 
{    
    { 
        .osd_char = ' ', 
        .data = 
        {
            0b00000000,
            0b00000000,
            0b00000000,
            0b00000000,
            0b00000000,
            0b00000000,
            0b00000000,
            0b00000000
        }
    },
    { 
        .osd_char = 'A', 
        .data = 
        {
            0b00000000,
            0b00011100,
            0b00100010,
            0b00100010,
            0b00111110,
            0b00100010,
            0b00100010,
            0b00000000
        }
    },
    { 
        .osd_char = 'B', 
        .data = 
        {
            0b00000000,
            0b00111100,
            0b00100010,
            0b00111100,
            0b00100010,
            0b00100010,
            0b00111110,
            0b00000000
        }
    },
    { 
        .osd_char = 'C', 
        .data = 
        {
            0b00000000,
            0b00011100,
            0b00100010,
            0b00100000,
            0b00100000,
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

void OSD_set_line_text(uint8_t line_index, const char* text)
{
    if (line_index >= OSD_LINES)
        return;

    for (int i = 0; i < OSD_CHARS_PER_LINE; i++)
    {
        osd_text[line_index][i] = i < strlen(text) ? text[i] : ' ';
    }
    osd_text[line_index][OSD_CHARS_PER_LINE] = '\0';
}

void OSD_update(void)
{
    int pos = 0;
    uint8_t color1 = 0x00;
    uint8_t color2 = 0x3C;
    for (int y = 0; y < OSD_LINES; y++)
    {
        for (int n = 0; n < OSD_CHAR_HEIGHT; n++)
        {
            for (int x = 0; x < OSD_CHARS_PER_LINE; x++)
            {
                char myChar = osd_text[y][x];
                uint8_t* char_data = get_char_data(myChar);
                for (int o = OSD_CHAR_WIDTH-1; o >= 0; o--)
                {
                    if (y == active_line)
                    {
                        framebuffer[pos++] = (((char_data[n] >> o) & 1) == 0) ? color2 : color1;
                    }
                    else
                    {
                        framebuffer[pos++] = (((char_data[n] >> o) & 1) == 0) ? color1 : color2;
                    }
                }
            }
        }
    }
}

// uint8_t OSD_get_width(void)
// {
//     return OSD_WIDTH;
// }

// uint8_t OSD_get_height(void)
// {
//     return OSD_HEIGHT;
// }

// uint8_t OSD_get_char_width(void)
// {
//     return OSD_CHAR_WIDTH;
// }

// uint8_t OSD_get_char_height(void)
// {
//     return OSD_CHAR_HEIGHT;
// }

// uint8_t OSD_get_line_count(void)
// {
//     return OSD_LINES;
// }

void OSD_change_line(int direction)
{
    active_line += direction;
    active_line = active_line >= OSD_LINES ? 0 : active_line;
    active_line = active_line < 0 ? OSD_LINES-1 : active_line;

    OSD_update();
}

uint8_t OSD_get_active_line(void)
{
    return (uint8_t)active_line;
}

uint8_t OSD_get_pixel(uint8_t x, uint8_t y)
{
    int pos = x + (y * OSD_WIDTH);
    if (pos >= sizeof(framebuffer))
        return 0;

    return framebuffer[pos];
}

uint8_t* OSD_get_framebuffer(void)
{
    return framebuffer;
}

//**********************************************************************************************
// PRIVATE FUNCTIONS
//**********************************************************************************************
static uint8_t* get_char_data(char lookup_char)
{
    int i = 0;
    while (osd_letters[i].osd_char != '\0')
    {
        if (osd_letters[i].osd_char == lookup_char)
            return osd_letters[i].data;
        
        i++;
    }
    
    // not found, return blank (first element)
    return osd_letters[0].data;
}
